el-dAna/hdtdcs/images/eeg_head_cap.jpg

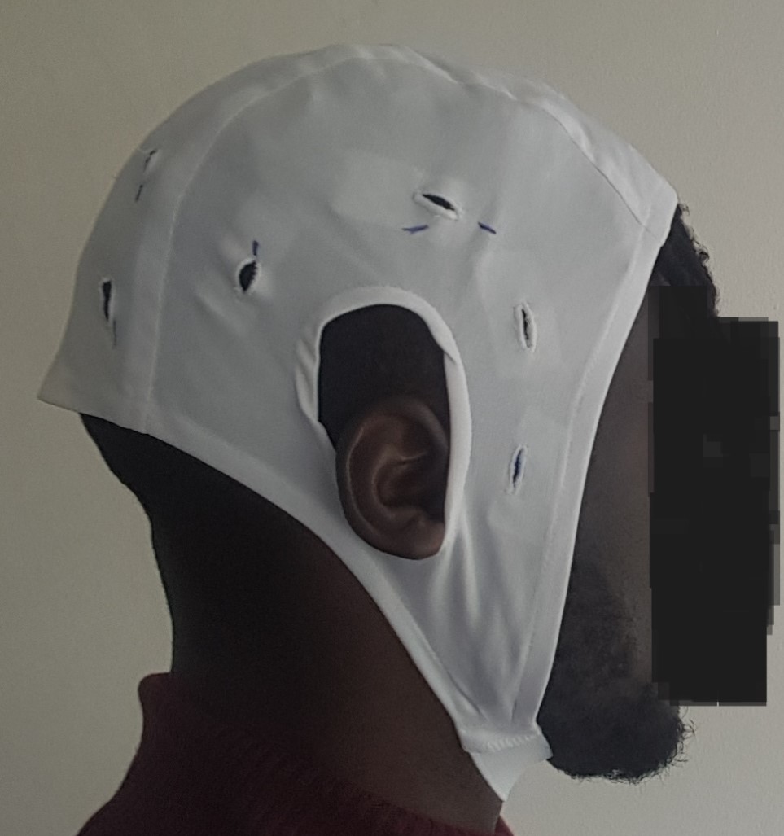
images/eeg_head_cap.jpg
