el-dAna/hdtdcs/images/electrode_cap_iso.jpg

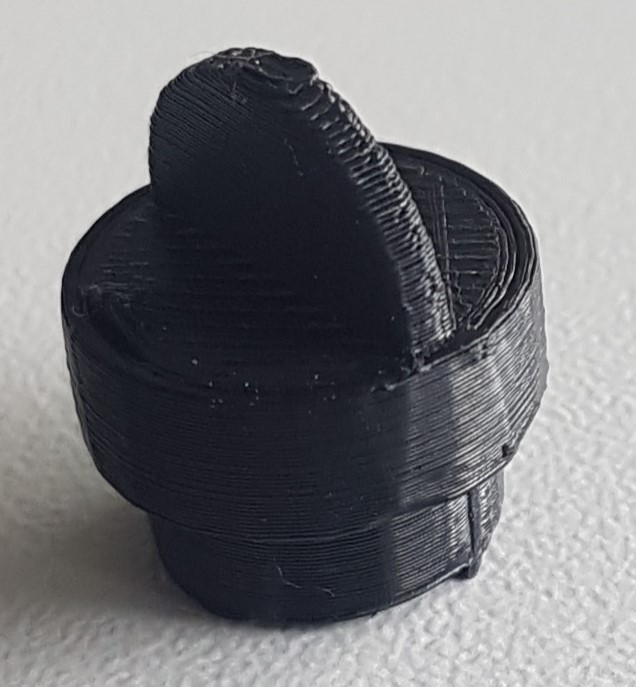
images/electrode_cap_iso.jpg
