el-dAna/hdtdcs/images/electrode_holder_bottom.jpg

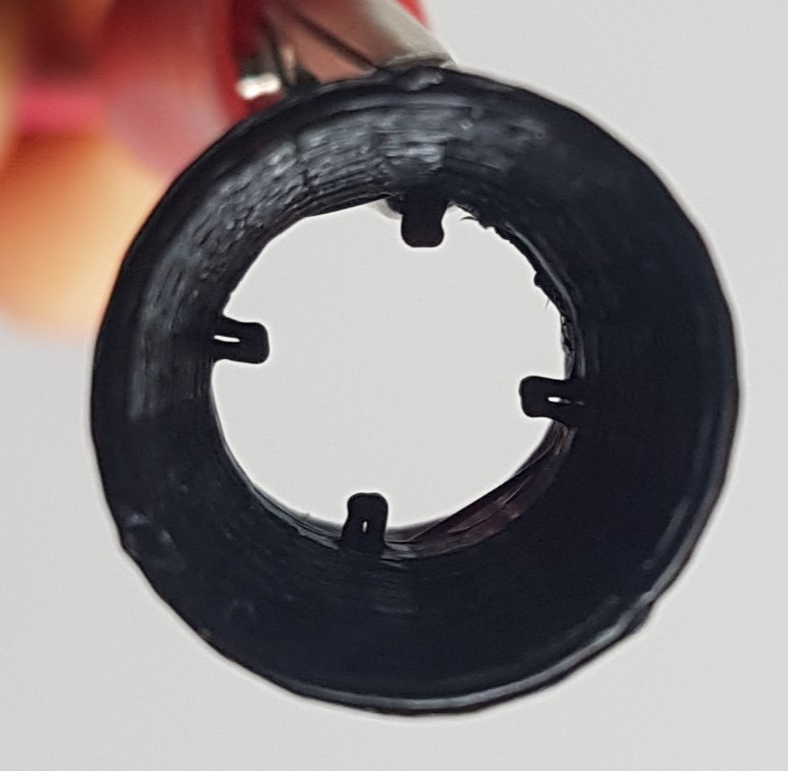
images/electrode_holder_bottom.jpg
