el-dAna/hdtdcs/images/electrode_holder_front.jpg

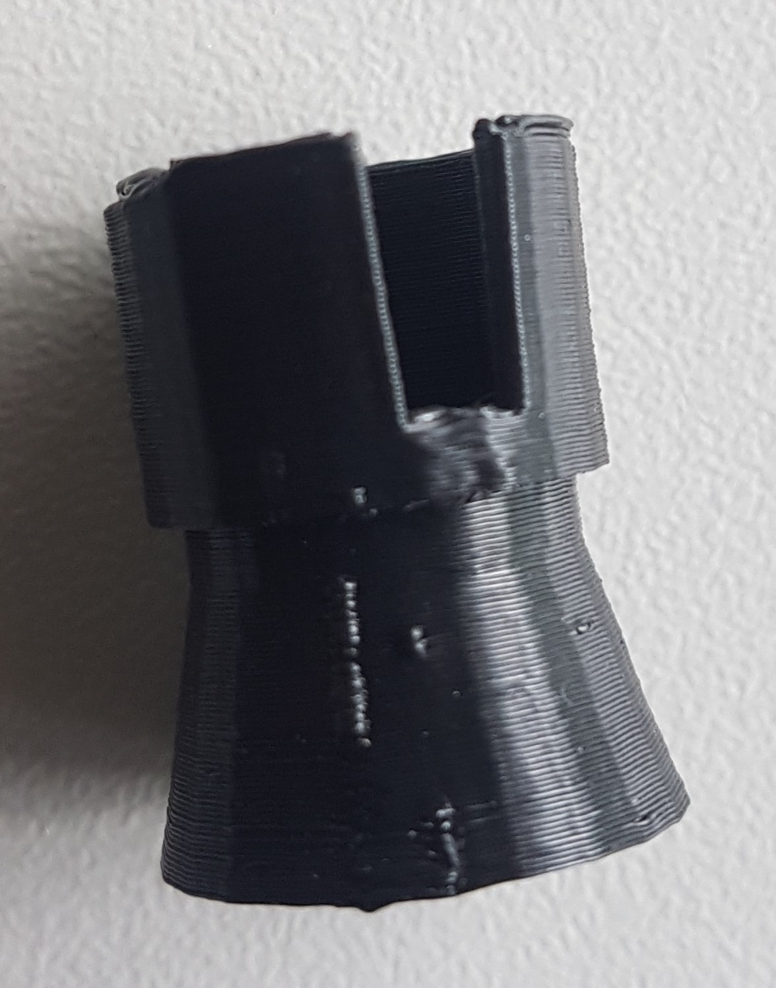
images/electrode_holder_front.jpg
