el-dAna/hdtdcs/images/electrode_holder_top.jpg

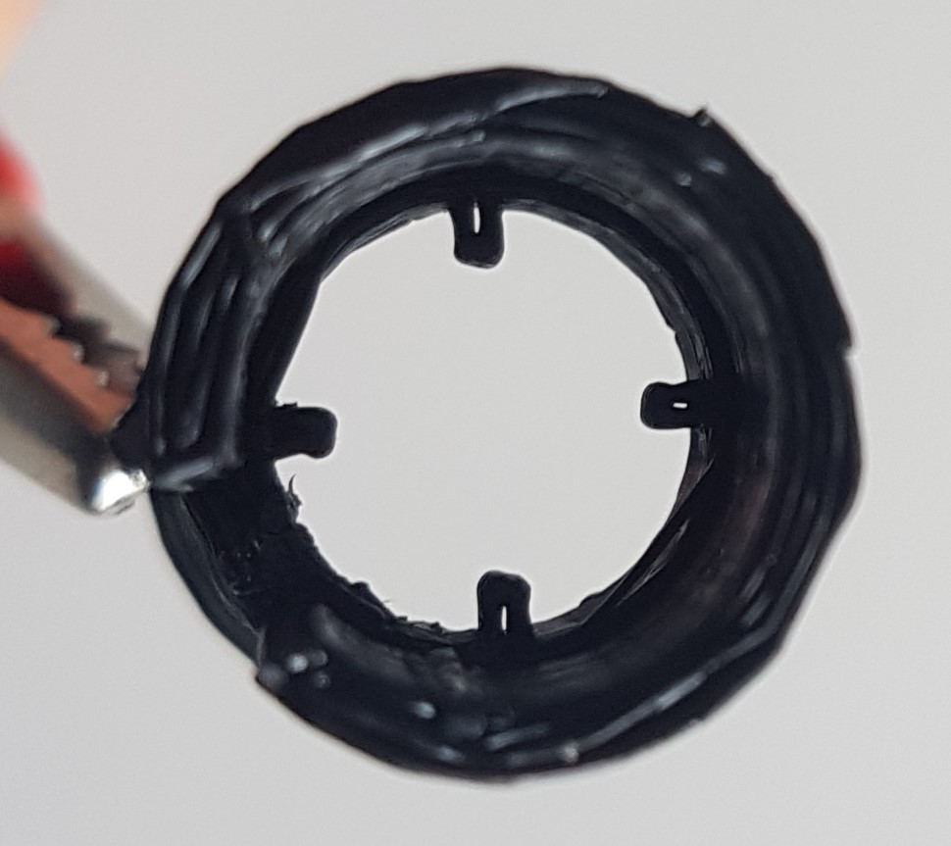
images/electrode_holder_top.jpg
