el-dAna/hdtdcs/images/electrode_potentiometer.jpg

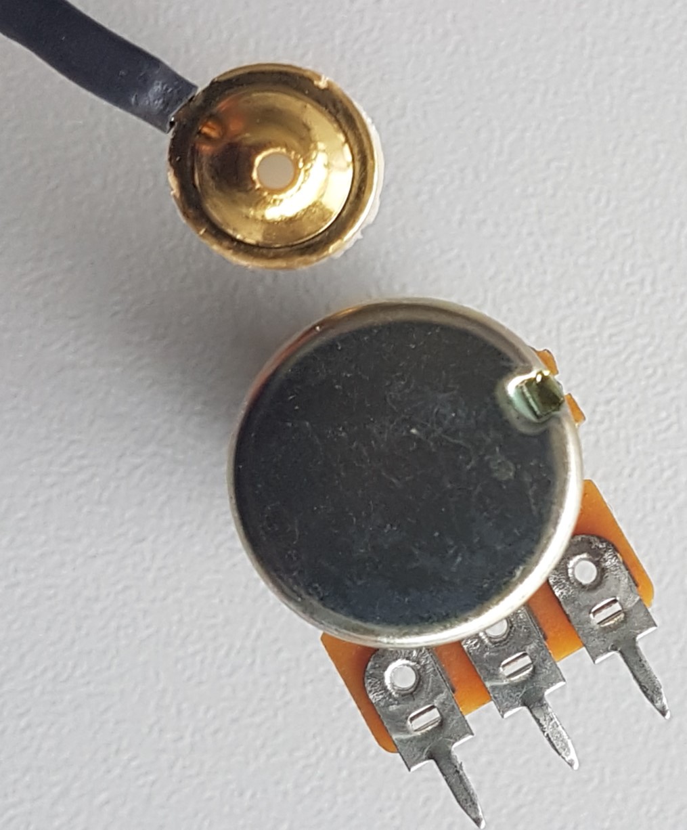
images/electrode_potentiometer.jpg
